046578139/Printing/preview/01_collar.png

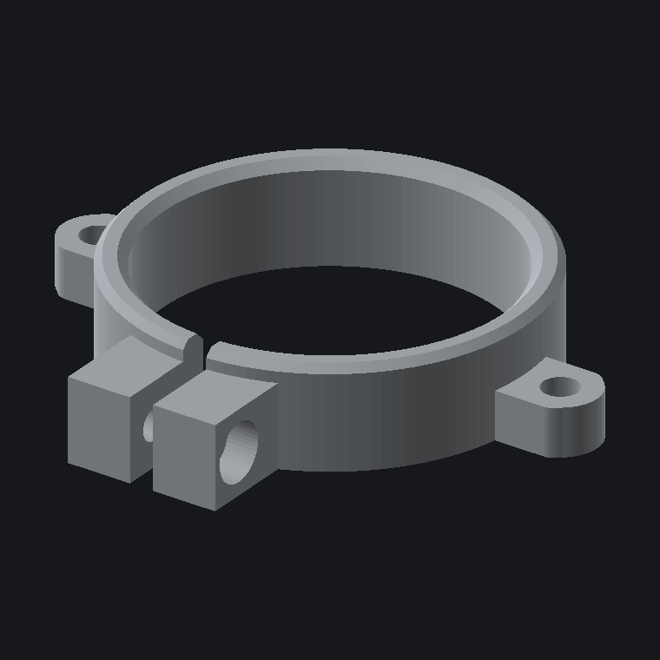
preview/01_collar.png
