046578139/Printing/preview/01b_collar_proto.png

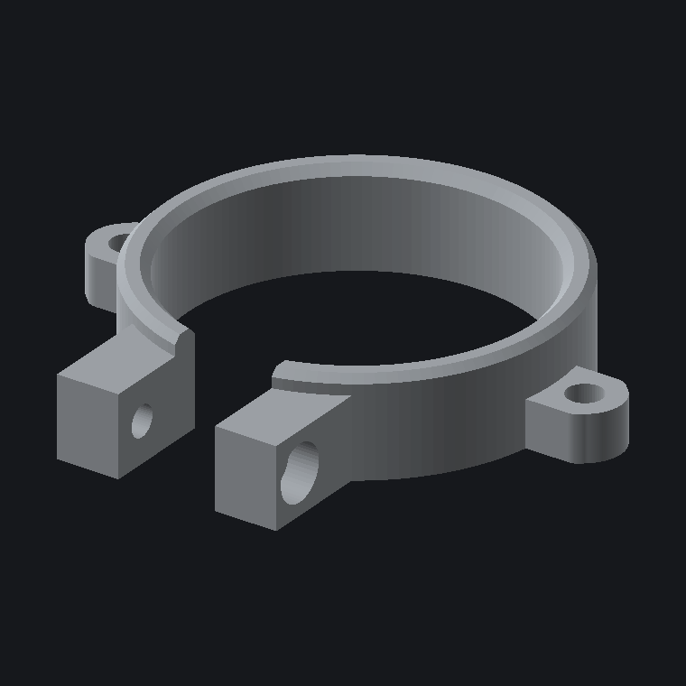
preview/01b_collar_proto.png
