046578139/Printing/preview/01c_collar_snap.png

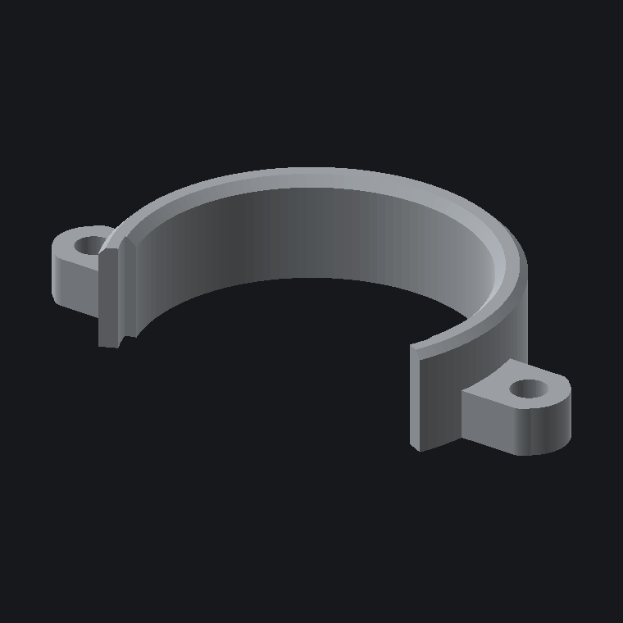
preview/01c_collar_snap.png
