046578139/Printing/preview/01g_collar_cinch.png

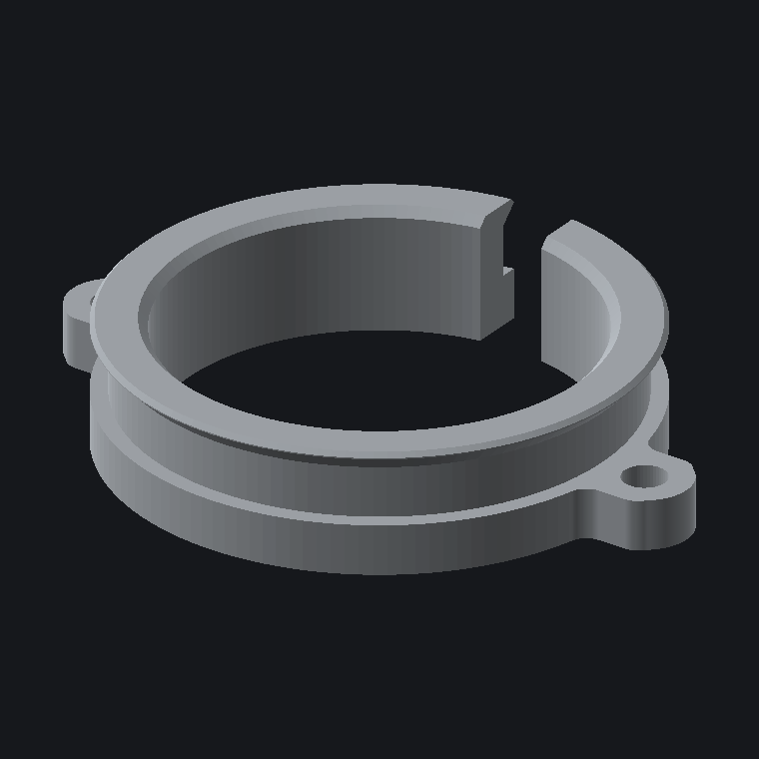
preview/01g_collar_cinch.png
