046578139/Printing/preview/04_flip_cap.png

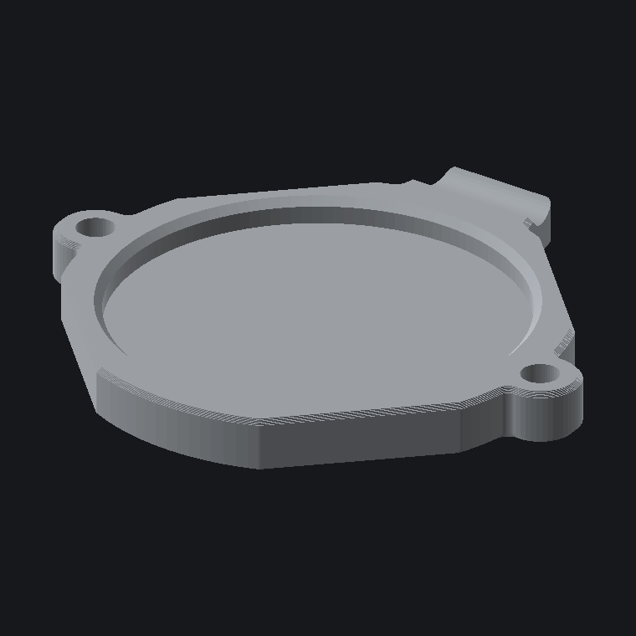
preview/04_flip_cap.png
