046578139/Printing/preview/05_gauge_shroud.png

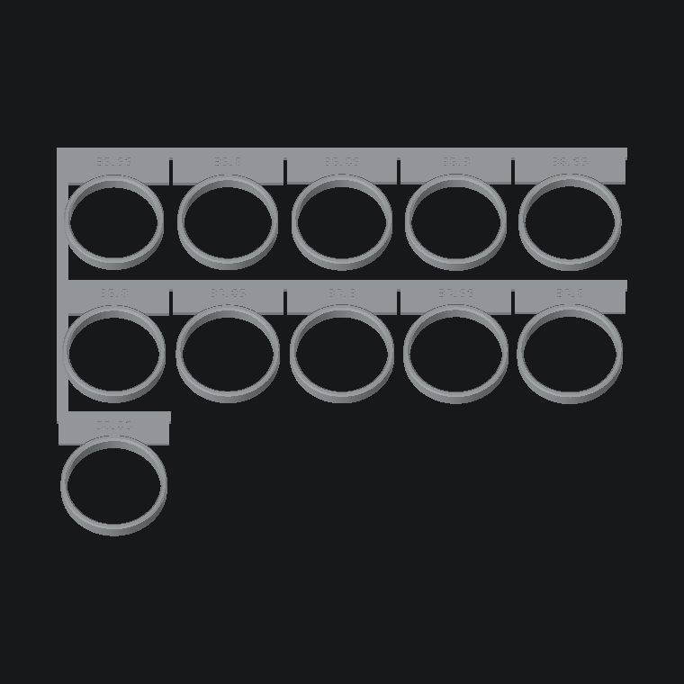
preview/05_gauge_shroud.png
