046578139/Printing/preview/05_gauge_shroud_nylon.png

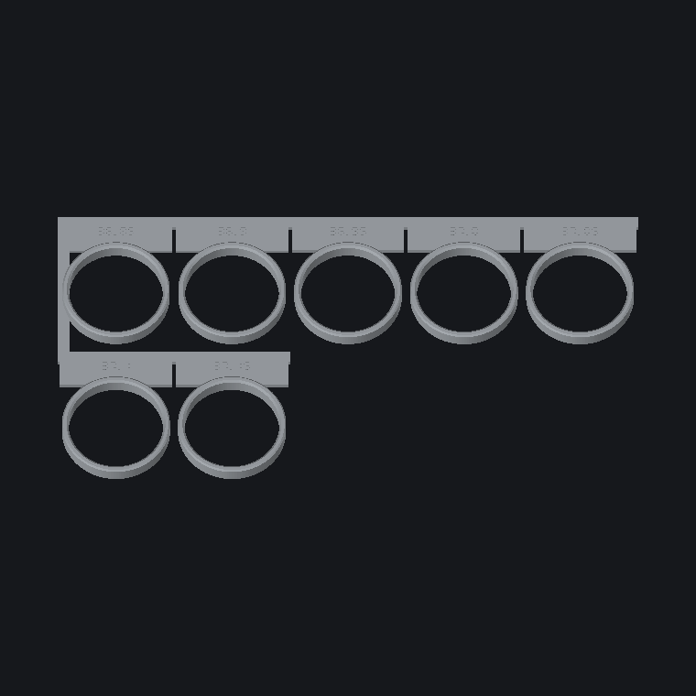
preview/05_gauge_shroud_nylon.png
