046578139/Printing/preview/05_gauge_shroud_petg2.png

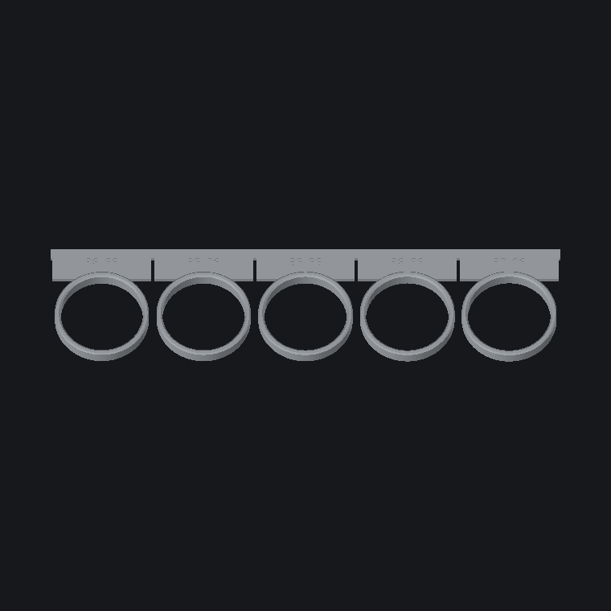
preview/05_gauge_shroud_petg2.png
