046578139/Printing/preview/06_gauge_collar.png

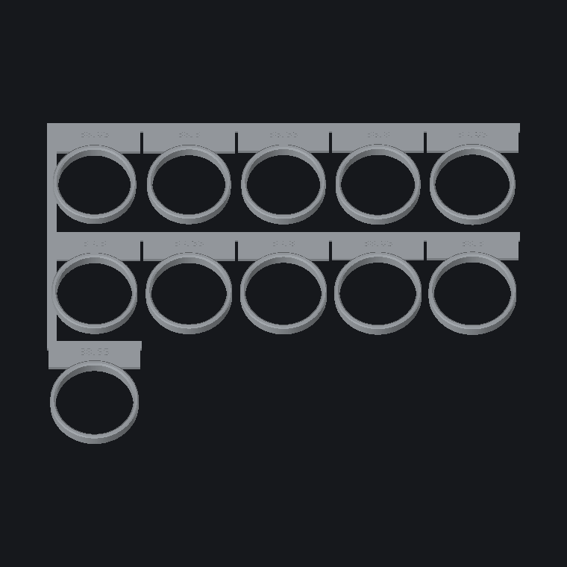
preview/06_gauge_collar.png
