046578139/Printing/stl/sweep/lever_36.00.stl

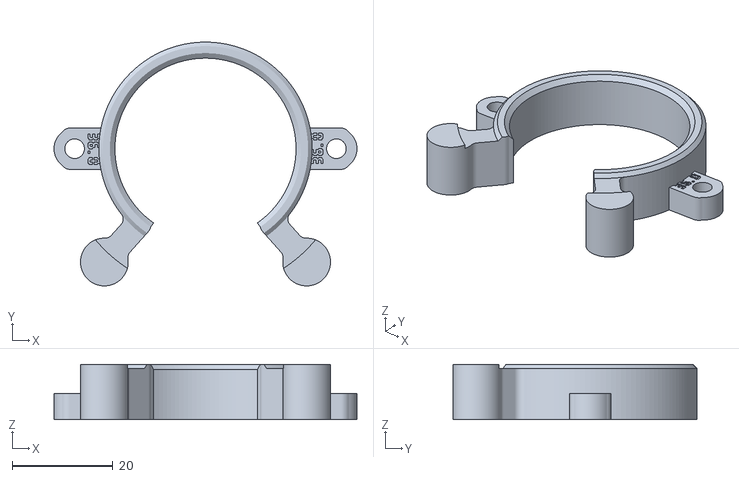
[picture p31: CAD file, 2026-09-21]
stl/sweep/lever_36.00.stl
60.2 x 48.5 x 11.0
