046578139/Printing/stl/04_inlay_hex.stl

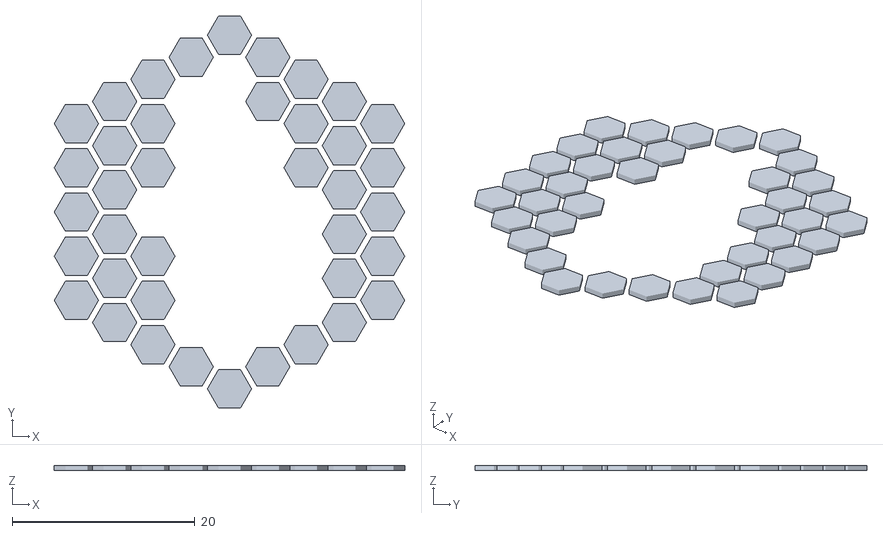
[picture p32: CAD file, 2026-09-22]
stl/04_inlay_hex.stl
38.4 x 42.9 x 0.6
