046578139/Printing/stl/sweep/lap_35.90.stl

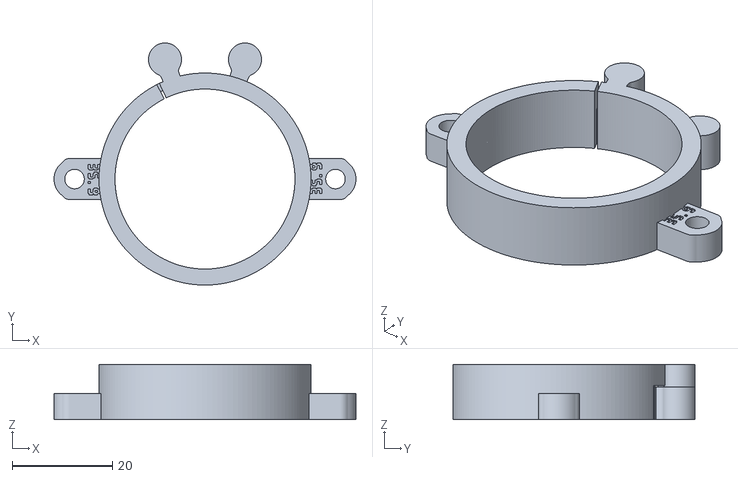
[picture p33: CAD file, 2026-09-21]
stl/sweep/lap_35.90.stl
60.2 x 48.3 x 11.0
