046578139/Printing/stl/04_inlay_mark.stl

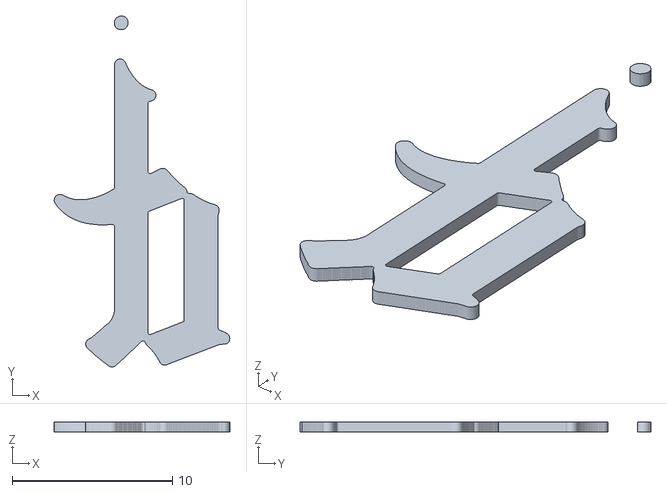
[picture p34: CAD file, 2026-09-22]
stl/04_inlay_mark.stl
10.9 x 21.9 x 0.6
