046578139/Printing/stl/04b_inlay_FUCK.stl

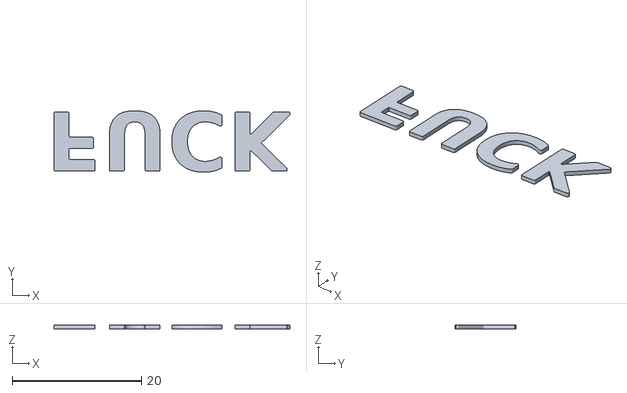
[picture p35: CAD file, 2026-09-22]
stl/04b_inlay_FUCK.stl
36.5 x 9.50 x 0.6
