046578139/Printing/stl/sweep/cinch_37.20.stl

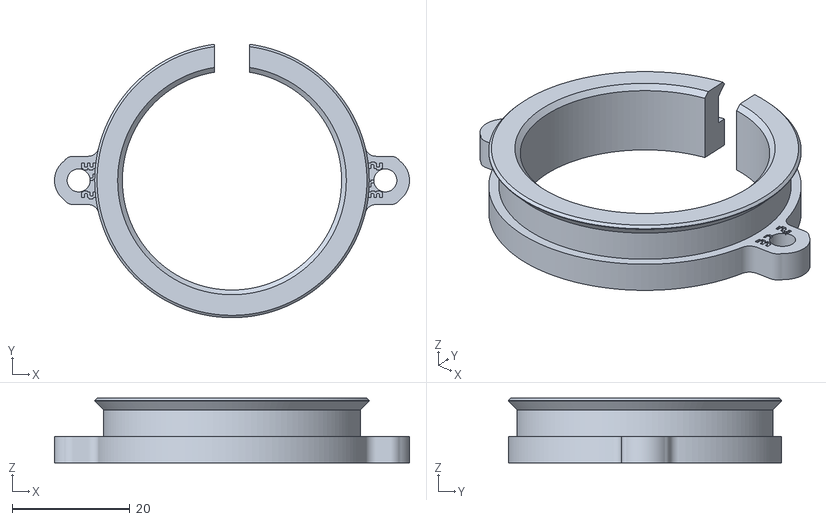
[picture p36: CAD file, 2026-09-21]
stl/sweep/cinch_37.20.stl
60.2 x 46.4 x 11.0
