046578139/Printing/stl/04b_inlay_hex_FUCK.stl

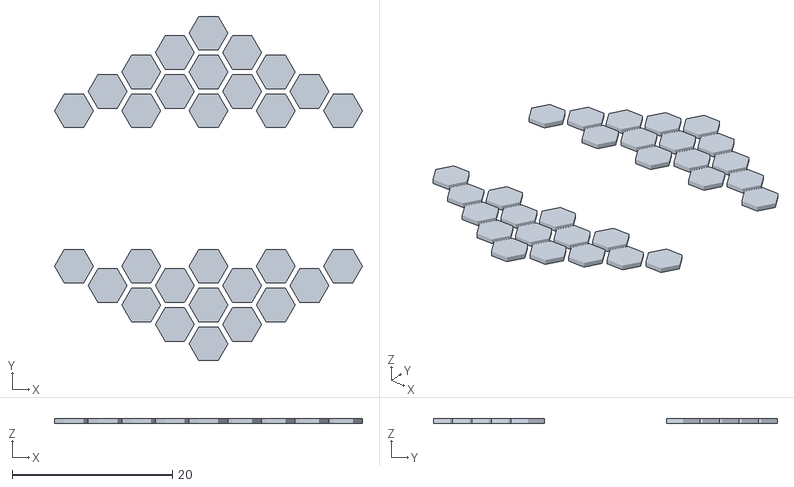
[picture p37: CAD file, 2026-09-22]
stl/04b_inlay_hex_FUCK.stl
38.4 x 42.9 x 0.6
