046578139/Printing/stl/sweep/pinch_36.50.stl

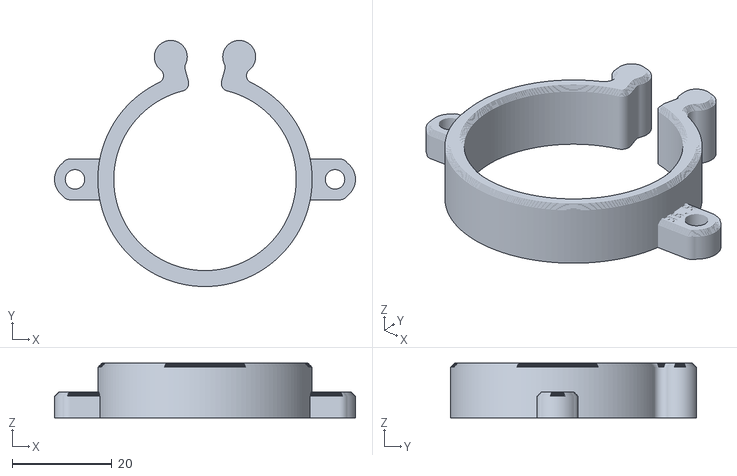
[picture p38: CAD file, 2026-09-21]
stl/sweep/pinch_36.50.stl
60.2 x 49.3 x 11.0
