046578139/Printing/stl/04c_flip_cap_YOU.stl

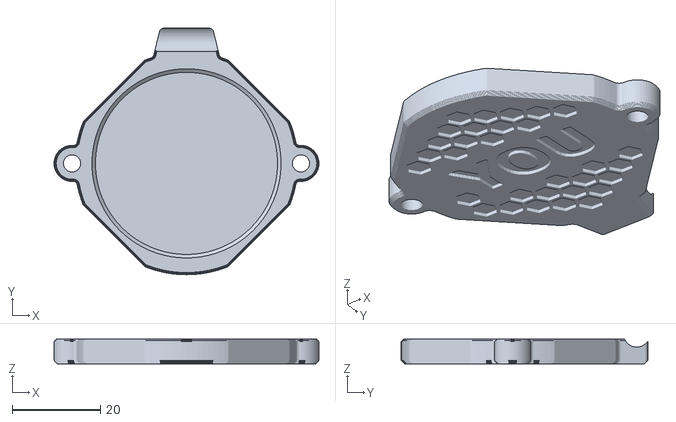
[picture p39: CAD file, 2026-09-22]
stl/04c_flip_cap_YOU.stl
60.2 x 56.0 x 5.60
