046578139/Printing/stl/sweep/cinch_39.20.stl

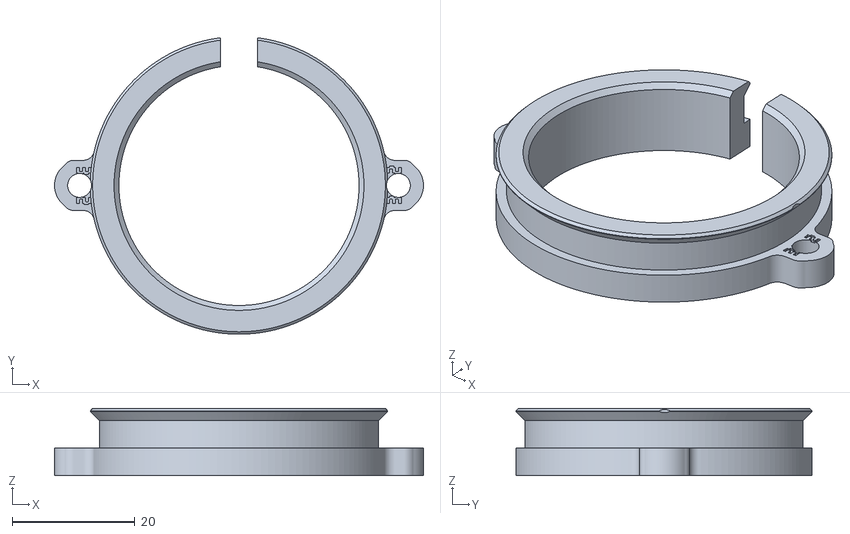
[picture p40: CAD file, 2026-09-21]
stl/sweep/cinch_39.20.stl
60.2 x 48.4 x 11.0
