046578139/Printing/stl/01g_collar_cinch.stl

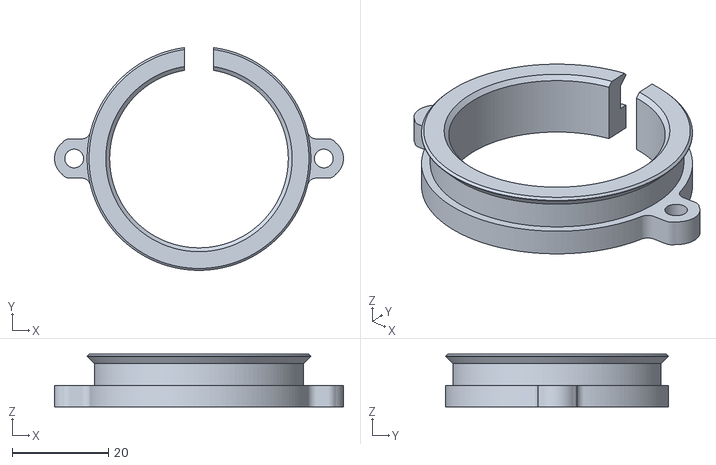
[picture p41: CAD file, 2026-09-21]
stl/01g_collar_cinch.stl
60.2 x 46.4 x 11.0
