046578139/Printing/stl/01b_collar_proto.stl

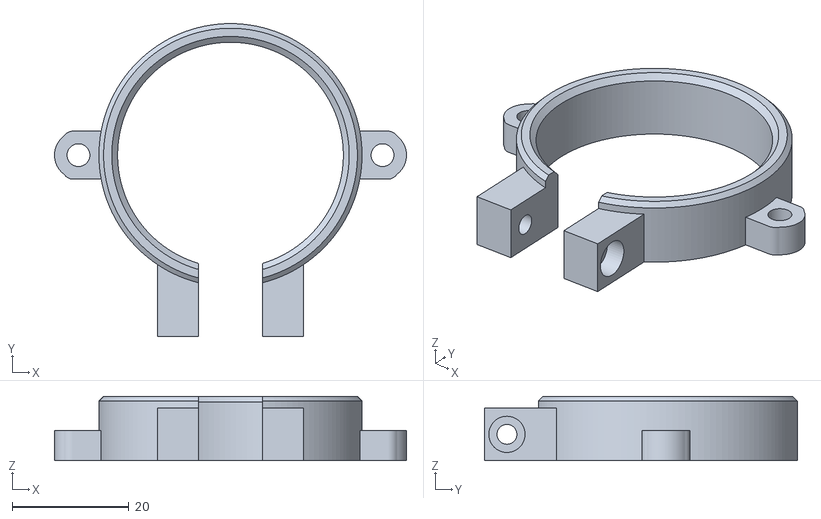
[picture p42: CAD file, 2026-09-21]
stl/01b_collar_proto.stl
60.2 x 53.5 x 11.0
