046578139/Printing/stl/sweep/pinch_36.80.stl

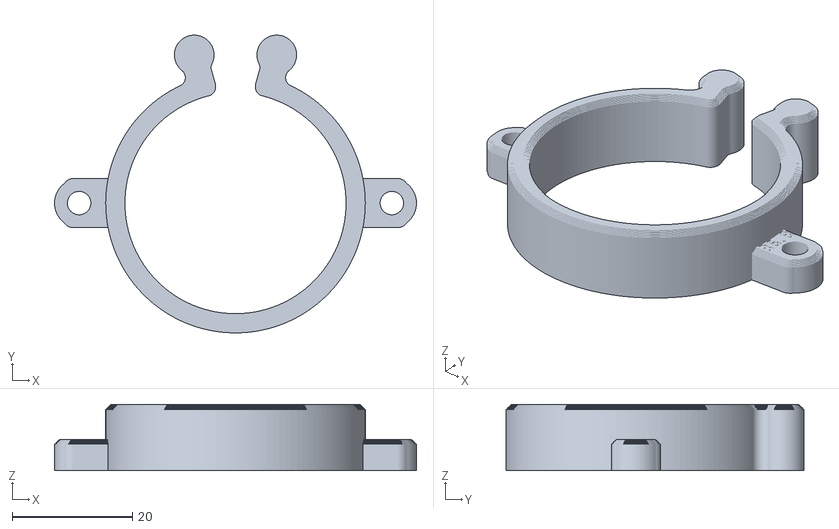
[picture p43: CAD file, 2026-09-21]
stl/sweep/pinch_36.80.stl
60.2 x 49.6 x 11.0
