046578139/Printing/stl/sweep/pinch_35.90.stl

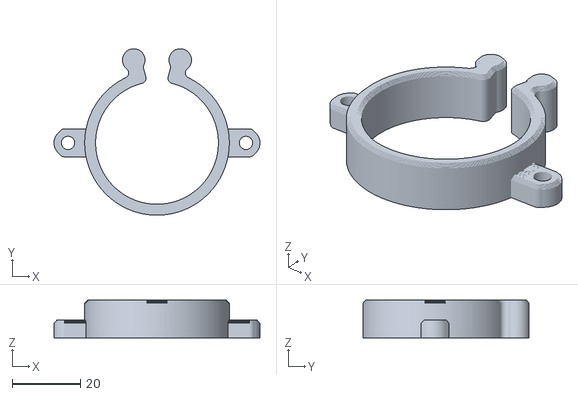
[picture p44: CAD file, 2026-09-21]
stl/sweep/pinch_35.90.stl
60.2 x 48.7 x 11.0
