046578139/Printing/stl/05_gauge_shroud.stl

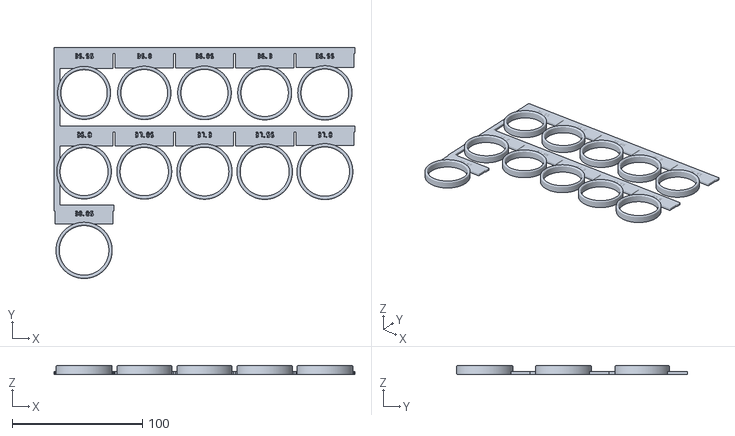
[picture p45: CAD file, 2026-09-21]
stl/05_gauge_shroud.stl
231.2 x 177.5 x 7.00
