046578139/Printing/stl/01_collar.stl

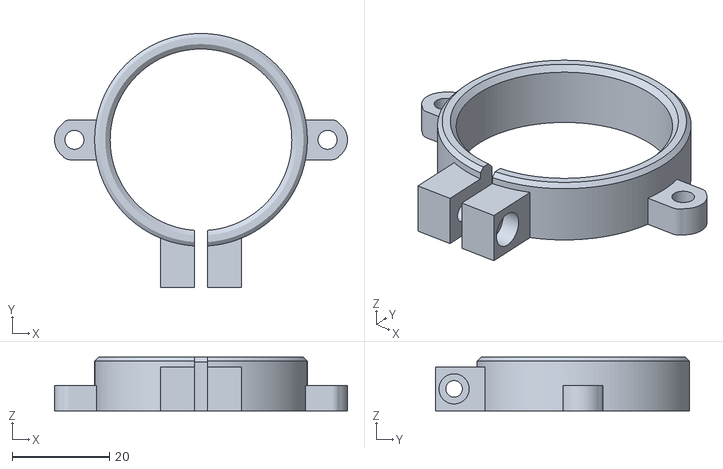
[picture p46: CAD file, 2026-09-21]
stl/01_collar.stl
60.2 x 52.2 x 11.0
