046578139/Printing/stl/02_killflash_housing.stl

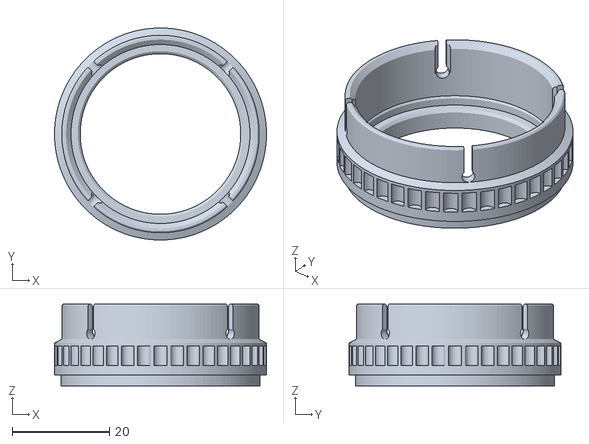
[picture p47: CAD file, 2026-09-21]
stl/02_killflash_housing.stl
43.6 x 43.6 x 16.8
