046578139/Printing/stl/sweep/kf_cell_03.4.stl

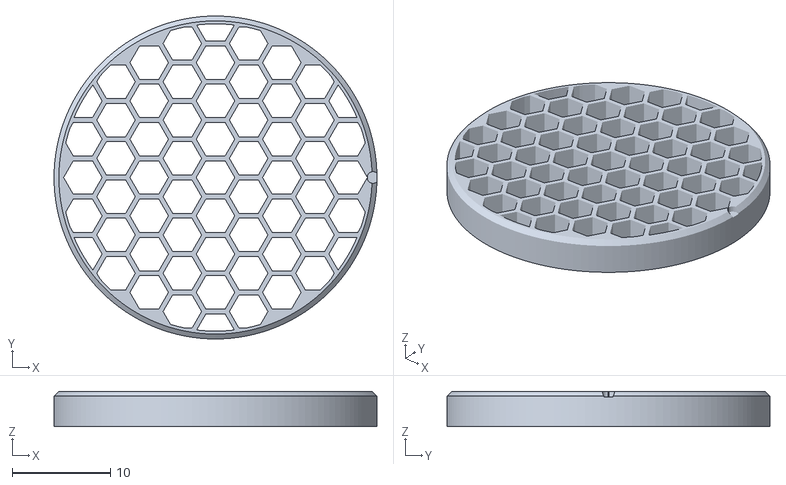
[picture p48: CAD file, 2026-09-21]
stl/sweep/kf_cell_03.4.stl
32.9 x 32.9 x 3.60
