046578139/Printing/stl/02b_killflash_housing_solid.stl

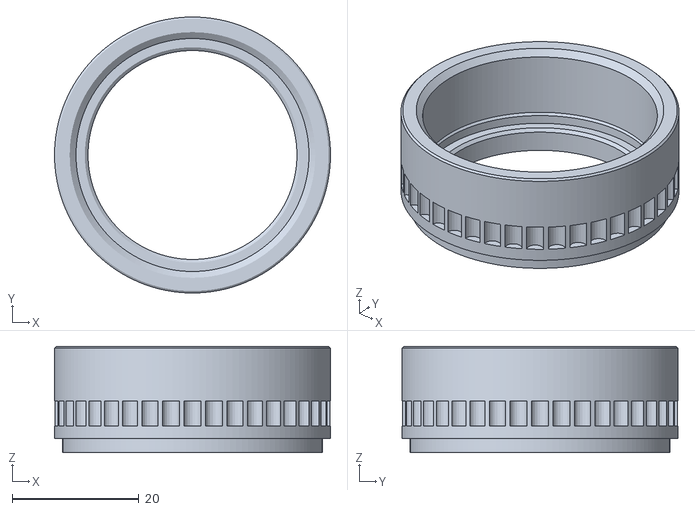
[picture p49: CAD file, 2026-09-21]
stl/02b_killflash_housing_solid.stl
43.6 x 43.6 x 16.8
