046578139/Printing/stl/sweep/kf_cell_05.0.stl

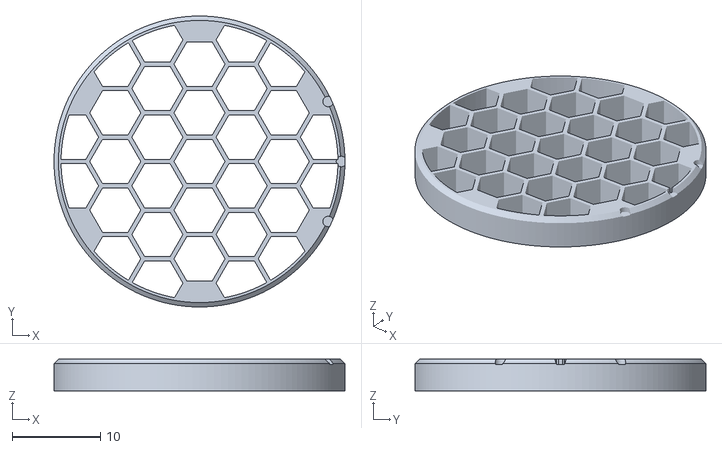
[picture p50: CAD file, 2026-09-21]
stl/sweep/kf_cell_05.0.stl
32.9 x 32.9 x 3.60
