046578139/Printing/stl/05_gauge_shroud_petg2.stl

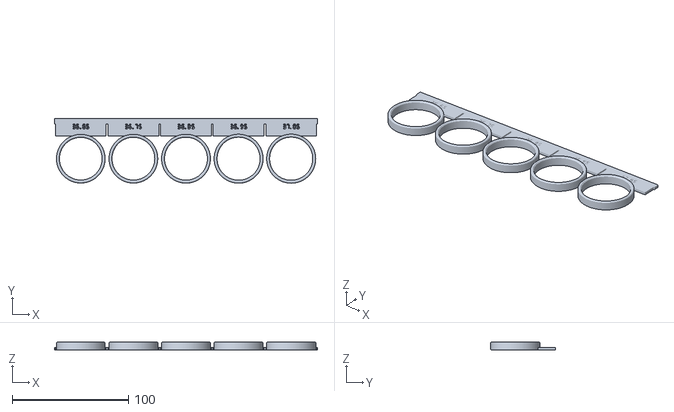
[picture p51: CAD file, 2026-09-21]
stl/05_gauge_shroud_petg2.stl
226.2 x 55.5 x 7.00
