046578139/Printing/stl/sweep/kf_od_32.80.stl

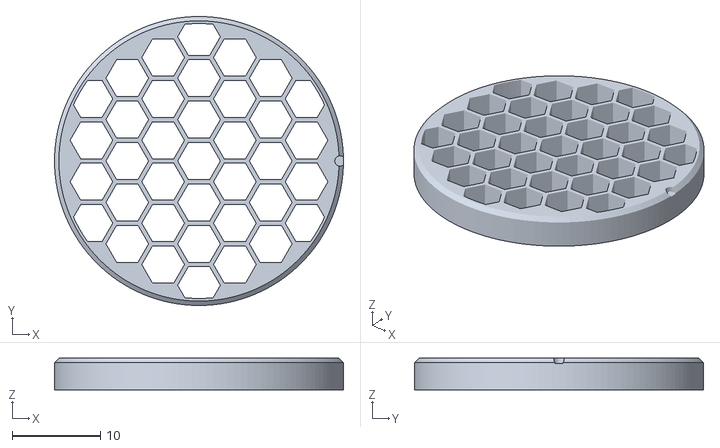
[picture p52: CAD file, 2026-09-21]
stl/sweep/kf_od_32.80.stl
32.8 x 32.8 x 3.60
