046578139/Printing/stl/sweep/kf_od_32.90.stl

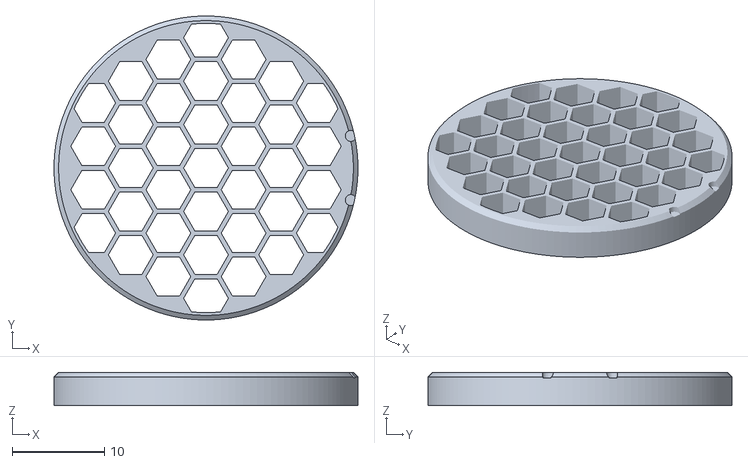
[picture p53: CAD file, 2026-09-21]
stl/sweep/kf_od_32.90.stl
32.9 x 32.9 x 3.60
