046578139/Printing/stl/07_gauge_killflash.stl

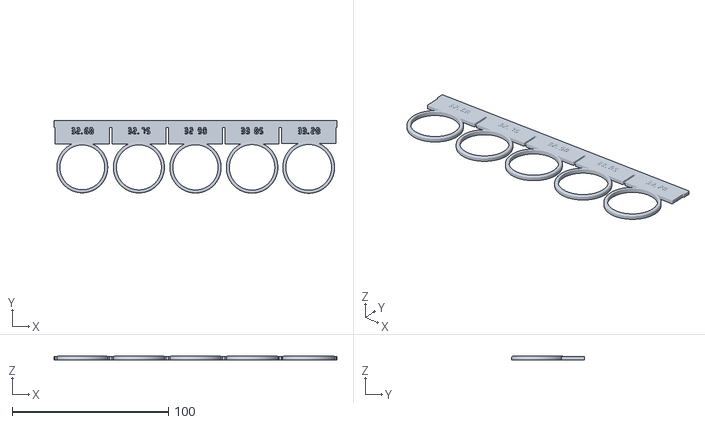
[picture p54: CAD file, 2026-09-21]
stl/07_gauge_killflash.stl
181.0 x 46.5 x 2.50
