046578139/Printing/stl/06_gauge_collar.stl

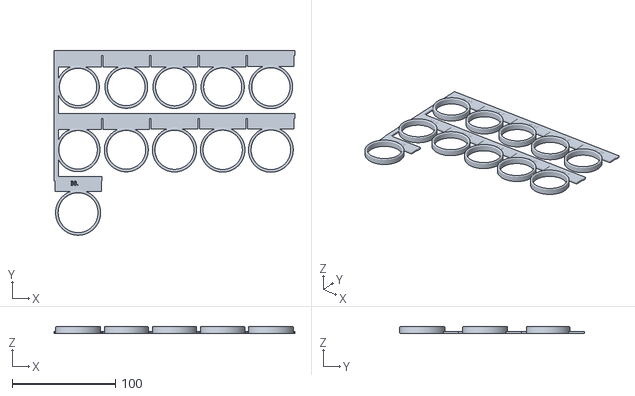
[picture p55: CAD file, 2026-09-21]
stl/06_gauge_collar.stl
233.8 x 179.0 x 7.00
