046578139/Printing/stl/06_gauge_collar_wide.stl

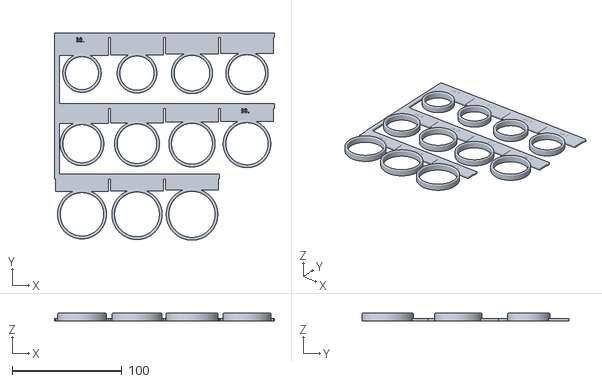
[picture p56: CAD file, 2026-09-21]
stl/06_gauge_collar_wide.stl
200.8 x 189.3 x 7.00
