046578139/Printing/stl/05_gauge_shroud_nylon.stl

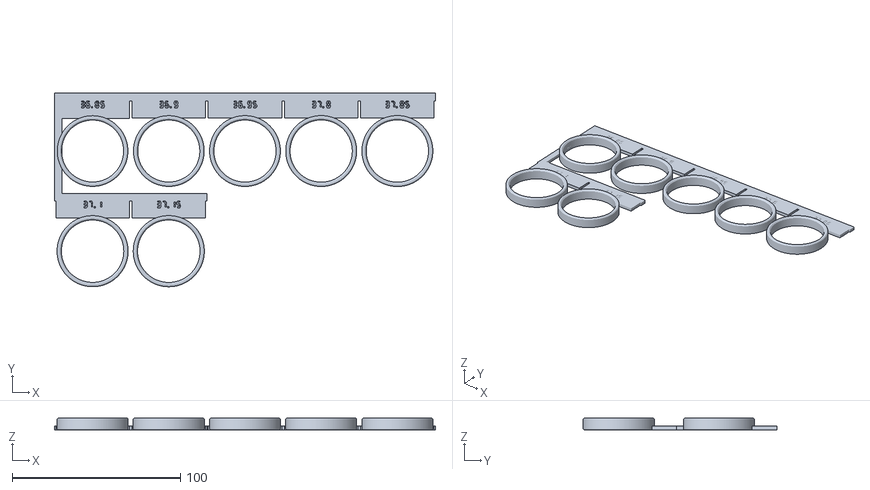
[picture p57: CAD file, 2026-09-21]
stl/05_gauge_shroud_nylon.stl
226.7 x 115.2 x 7.00
